cr1tbit/laptop2usb/img/img2.jpg

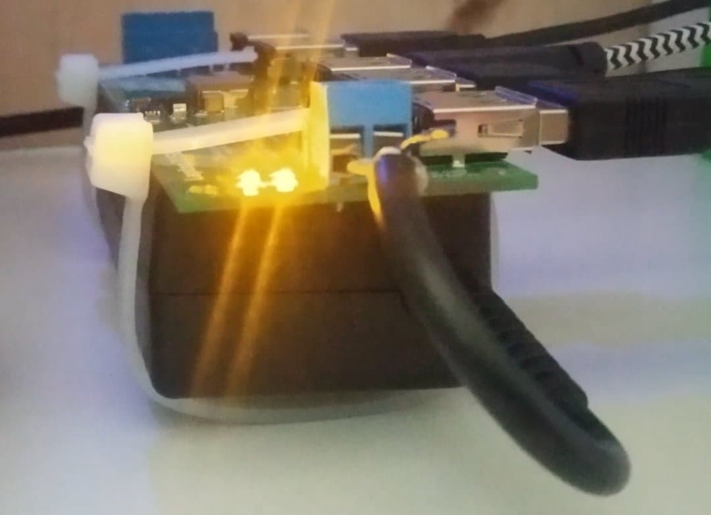
img/img2.jpg
